chrfriese123/Time-in-Words/arduino/definitions.h

#ifndef __NPDEF_H_
#define __NPDEF_H_

uint8_t welcomeScreen[5][7] = { 
  {  6,  10,  41,  42,  43,  44,  52},
  { 64,  65,  74,  75,  86,  87, 254},
  { 85, 254, 254, 254, 254, 254, 254},
  { 97,  98,  99, 254, 254, 254, 254},
  {106, 254, 254, 254, 254, 254, 254}
};


// Die Matrix definiert die Spalten/Zeilen Koordinaten, der LED Paare, die für das jeweilige Element angehen sollen
// LED 1 = 2*num
// LED 2 = 2*num+1
uint8_t ledKoordinate[26][7] = {
// 0: ES IST
  {  4,  5,    7,   8,   9, 254, 254},
// 1: EINS (Stunde)
  {107, 108, 109, 110, 254, 254, 254},
// 2: ZWEI (Stunde) 
  { 66,  67,  68,  69, 254, 254, 254},
// 3: DREI (Stunde)
  { 99, 100, 101, 102, 254, 254, 254},
// 4: VIER (Stunde) 
  { 70,  71,  72,  73, 254, 254, 254},
// 5: FÜNF (Stunde) 
  { 81,  82,  83,  84, 254, 254, 254},
// 6: SECHS (Stunde) 
  { 76,  77,  78,  79,  80, 254, 254},
// 7: SIEBEN (Stunde)
  { 53,  54,  55,  56,  57,  58, 254},
// 8: ACHT (Stunde)
  { 88,  89,  90,  91, 254, 254, 254},
// 9: NEUN (Stunde)
  { 95,  96,  97,  98, 254, 254, 254},
// 10: ZEHN (Stunde)
  { 92,  93,  94,  95, 254, 254, 254},
// 11: ELF (Stunde)
  {111, 112, 113, 254, 254, 254, 254},
// 12: ZWÖLF (Stunde)
  { 59,  60,  61,  62,  63, 254, 254},
// 13: "1" (Eckpunkt Minute)
  {  2, 254, 254, 254, 254, 254, 254},
// 14: "2" (Eckpunkt Minute)
  {  2,   1, 254, 254, 254, 254, 254},
// 15: "3" (Eckpunkt Minute)
  {  2,   1,   0, 254, 254, 254, 254},
// 16: "4" (Eckpunkt Minute)
  {  2,   1,   0,   3, 254, 254, 254},
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
{ 13, 14, 17, 23, 24, 99, 99  }, // 37
{ 13, 14, 15, 17, 23, 24, 99  }, // 38
{ 13, 14, 15, 16, 17, 23, 24  }, // 39
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
};

//Testbildschirm, nur alle "E" werden angeleuchtet
uint8_t testScreen[18] = {4,24,28,32,35,52,55,57,67,72,75,77,86,93,96,101,113,110};
#endif
